jpruiz84/relojma32-2/Folleto/Fotos/2012-06-14 12.34.01.jpg

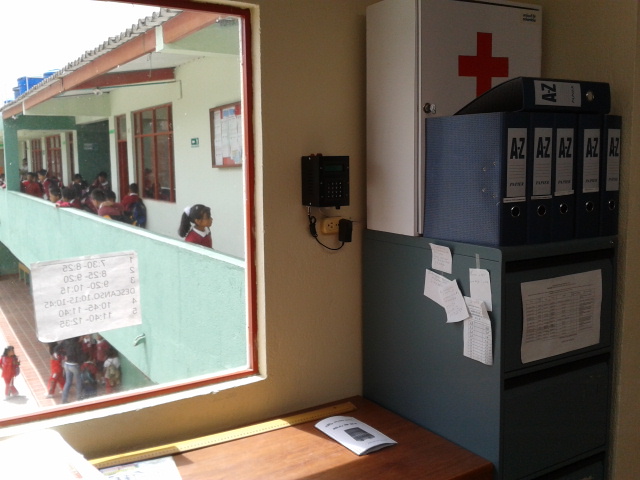
Folleto/Fotos/2012-06-14 12.34.01.jpg
