jpruiz84/relojma32-2/Folleto/Fotos/cerca.png

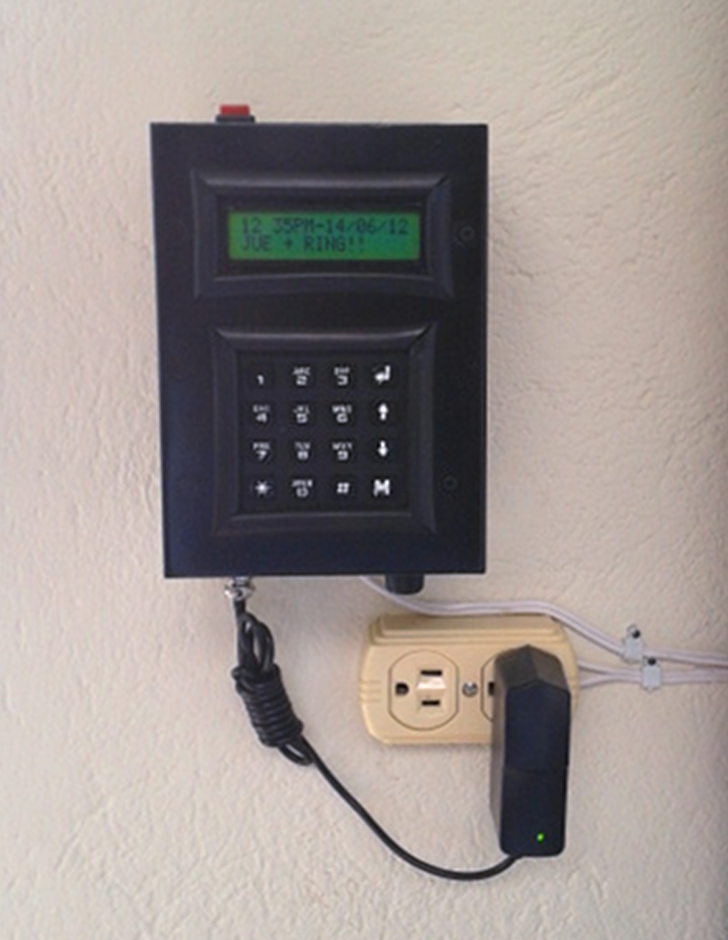
Folleto/Fotos/cerca.png
