jpruiz84/relojma32-2/Folleto/partes/firma.png

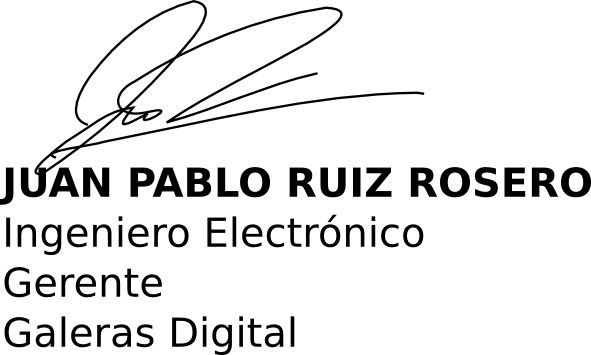
Folleto/partes/firma.png
