jpruiz84/relojma32-2/Folleto/partes/tapa.png

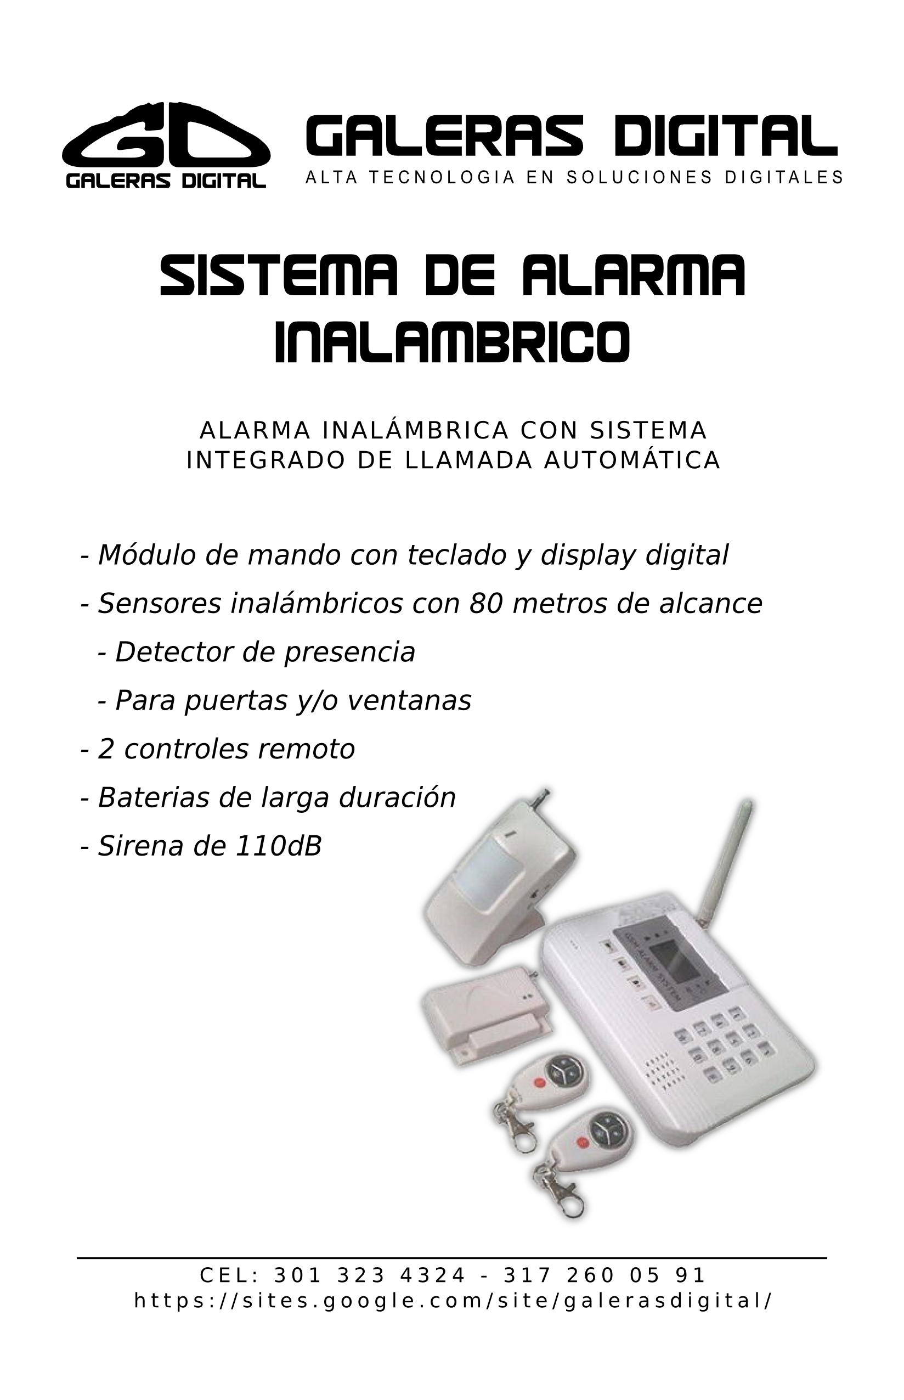
Folleto/partes/tapa.png
