jpruiz84/relojma32-2/Folleto/partes/timbre-13298.jpg

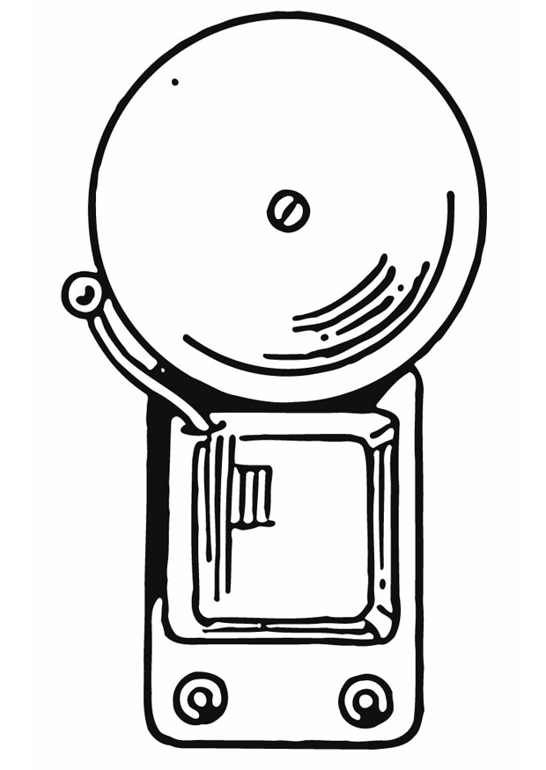
Folleto/partes/timbre-13298.jpg
