jpruiz84/relojma32-2/Pagina/fotofrente 300.jpg

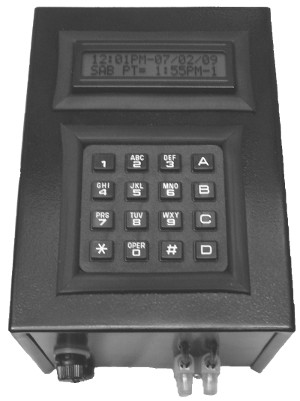
Pagina/fotofrente 300.jpg
